TrasnaCellular/LEXI-ADAM-Arduino-shield-HW/shield_design_library/3D/DRL0006A.stp

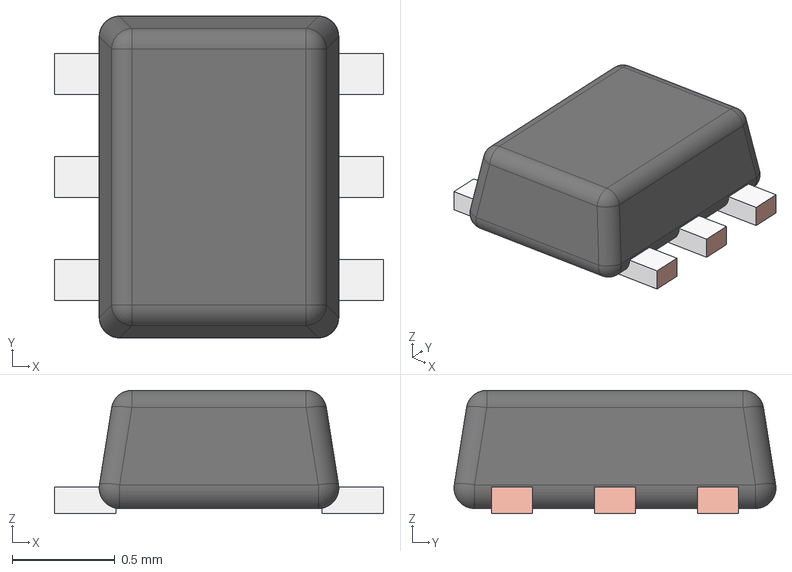
[picture p16: CAD file, 2026-05-26]
shield_design_library/3D/DRL0006A.stp
1.60 x 1.57 x 0.6 mm
FRAME-DRL0006A
BODY-SOT
PIN1-ID
