TrasnaCellular/LEXI-ADAM-Arduino-shield-HW/shield_design_library/3D/RES_SMA-A0102FTDL10R_TEC.step

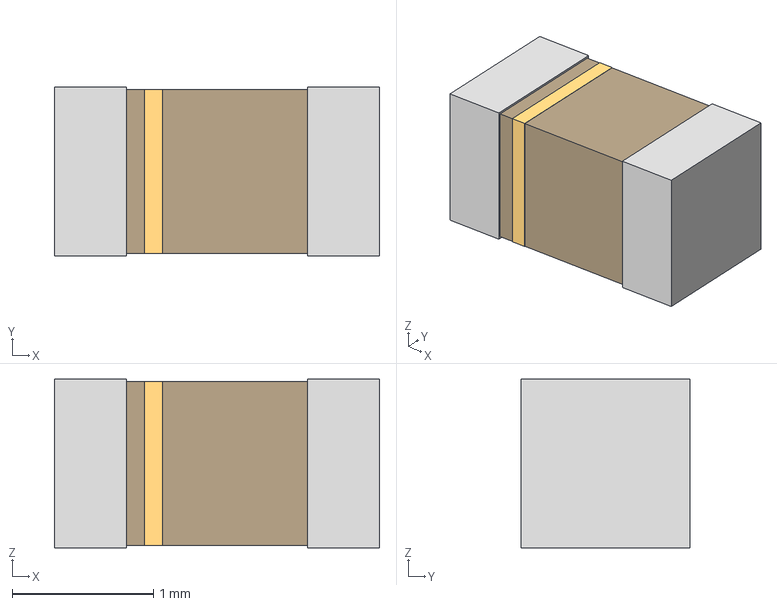
[picture p17: CAD file, 2026-05-26]
shield_design_library/3D/RES_SMA-A0102FTDL10R_TEC.step
2.30 x 1.19 x 1.19 mm
