TrasnaCellular/LEXI-ADAM-Arduino-shield-HW/shield_design_library/3D/SSW-106-03-G-S.stp

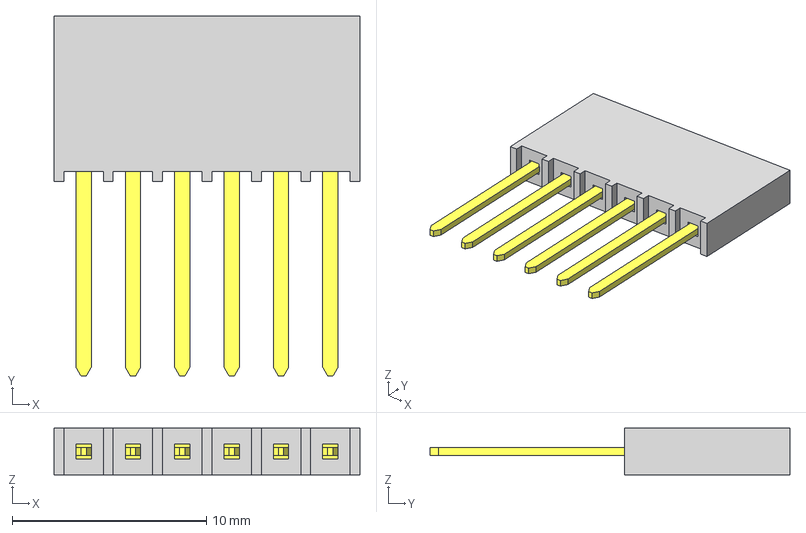
[picture p18: CAD file, 2026-05-26]
shield_design_library/3D/SSW-106-03-G-S.stp
15.7 x 18.5 x 2.41 mm
T1SSW-106-03-L-S
P2SSW-106-03-L-S
