TrasnaCellular/LEXI-ADAM-Arduino-shield-HW/shield_design_library/3D/Crystal_SMD_Abracon_ABM3B-4Pin_5.0x3.2mm.step

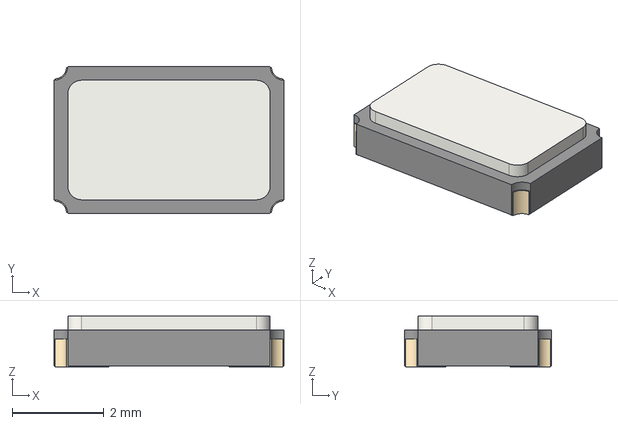
[picture p19: CAD file, 2026-05-26]
shield_design_library/3D/Crystal_SMD_Abracon_ABM3B-4Pin_5.0x3.2mm.step
5.00 x 3.20 x 1.10 mm
