TrasnaCellular/LEXI-ADAM-Arduino-shield-HW/shield_design_library/3D/IND_BLM18_0603_MUR.step

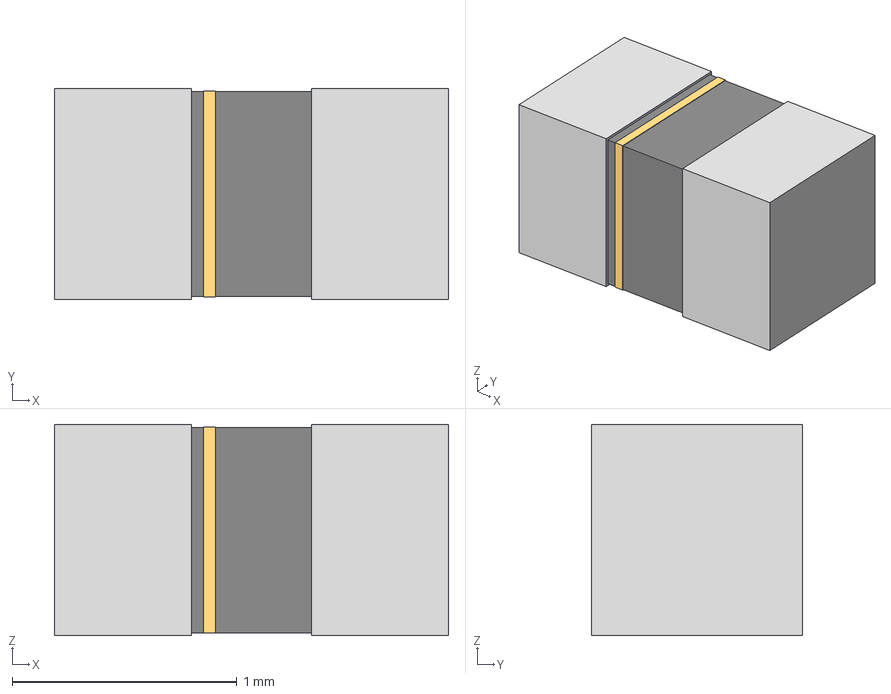
[picture p20: CAD file, 2026-05-26]
shield_design_library/3D/IND_BLM18_0603_MUR.step
1.75 x 0.94 x 0.94 mm
