TrasnaCellular/LEXI-ADAM-Arduino-shield-HW/shield_design_library/3D/LED_LTST-C190_LTO.step

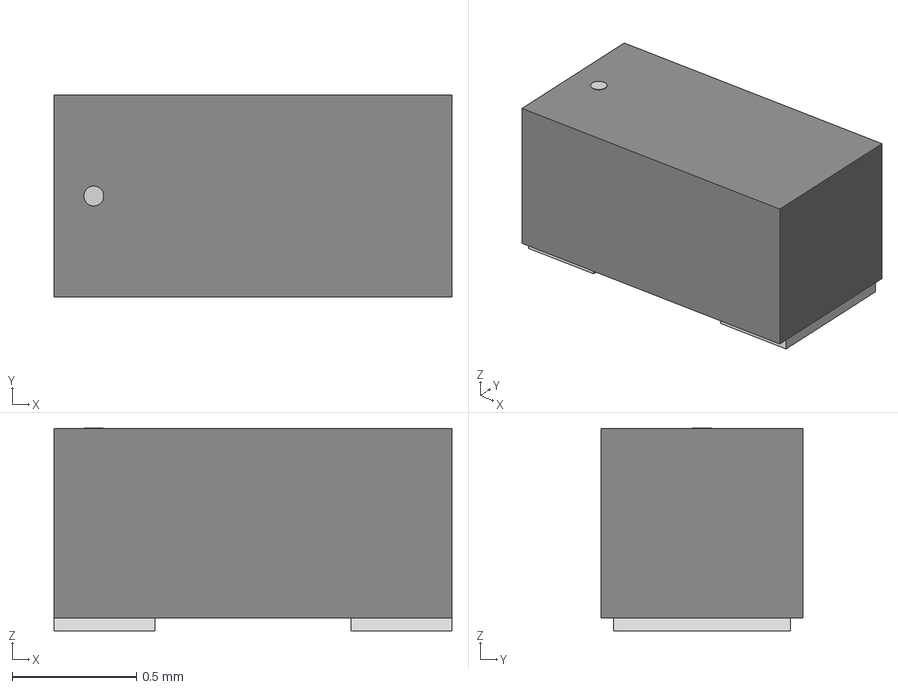
[picture p21: CAD file, 2026-05-26]
shield_design_library/3D/LED_LTST-C190_LTO.step
1.60 x 0.812 x 0.815 mm
