TrasnaCellular/LEXI-ADAM-Arduino-shield-HW/shield_design_library/3D/MICROPAK6_1X1P45_ONS.step

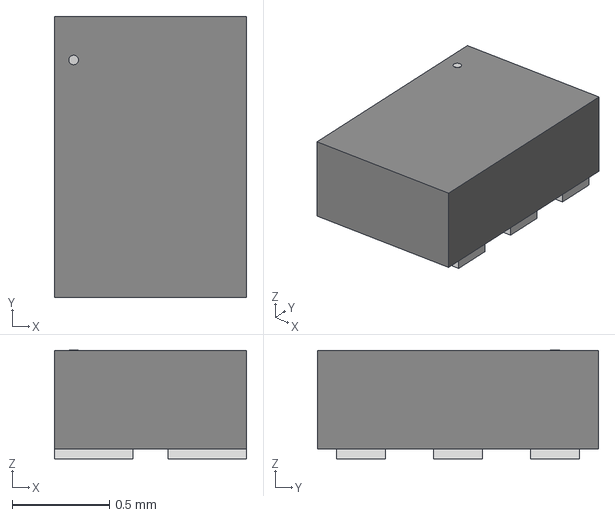
[picture p22: CAD file, 2026-05-26]
shield_design_library/3D/MICROPAK6_1X1P45_ONS.step
0.99 x 1.45 x 0.561 mm
