TrasnaCellular/LEXI-ADAM-Arduino-shield-HW/shield_design_library/3D/PESD0402-140_LTF.step

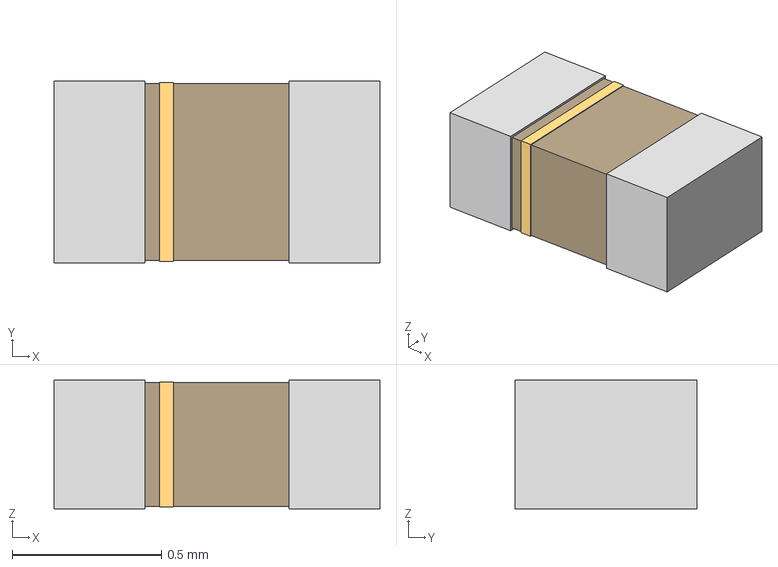
[picture p23: CAD file, 2026-05-26]
shield_design_library/3D/PESD0402-140_LTF.step
1.09 x 0.61 x 0.432 mm
