TrasnaCellular/LEXI-ADAM-Arduino-shield-HW/shield_design_library/3D/21-0076E_MXM.step

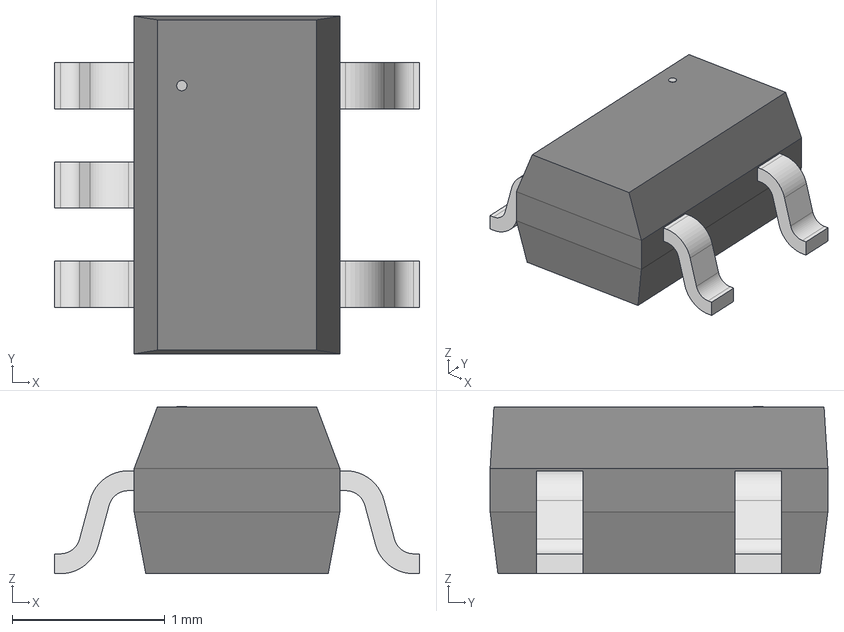
[picture p24: CAD file, 2026-05-26]
shield_design_library/3D/21-0076E_MXM.step
2.39 x 2.21 x 1.09 mm
