TrasnaCellular/LEXI-ADAM-Arduino-shield-HW/shield_design_library/3D/CT3151-0.stp

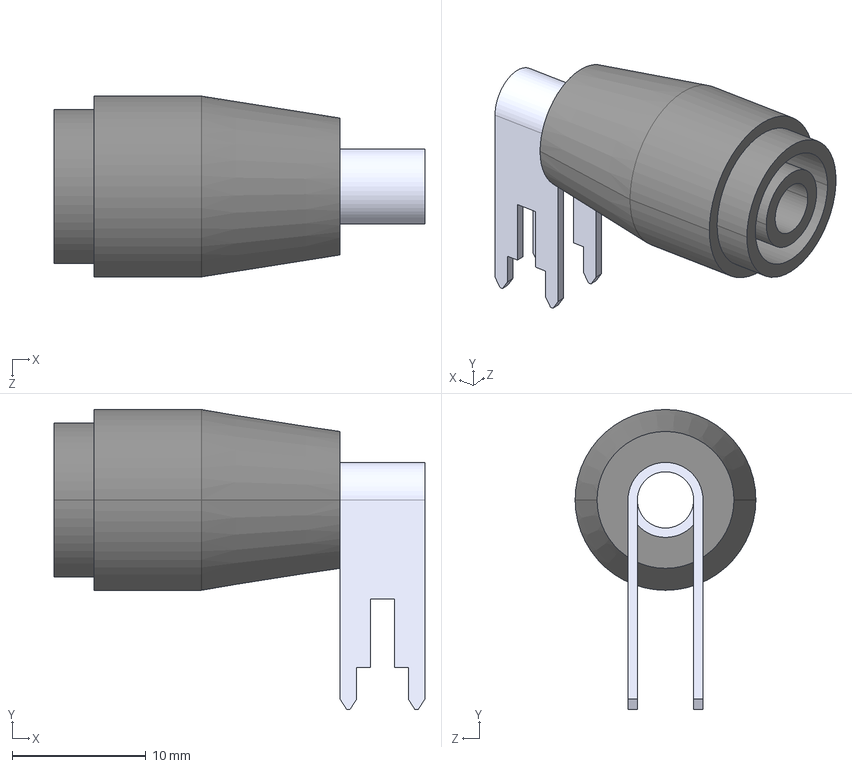
[picture p25: CAD file, 2026-05-26]
shield_design_library/3D/CT3151-0.stp
27.7 x 22.4 x 13.5 mm
