TrasnaCellular/LEXI-ADAM-Arduino-shield-HW/shield_design_library/3D/SC-88A-5_1P35X2P2_ONS.step

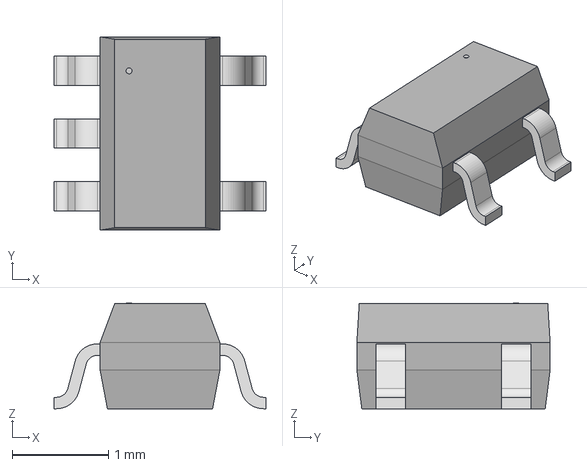
[picture p26: CAD file, 2026-05-26]
shield_design_library/3D/SC-88A-5_1P35X2P2_ONS.step
2.20 x 2.01 x 1.09 mm
