TrasnaCellular/LEXI-ADAM-Arduino-shield-HW/shield_design_library/3D/SOT-23-5_ONS.step

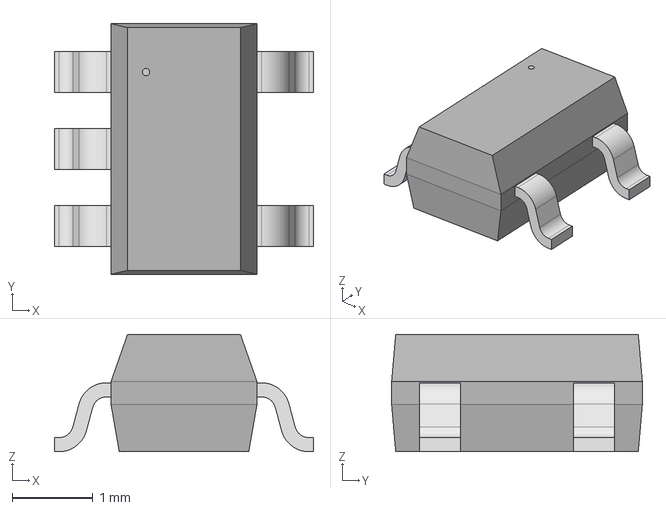
[picture p27: CAD file, 2026-05-26]
shield_design_library/3D/SOT-23-5_ONS.step
3.20 x 3.10 x 1.45 mm
