TrasnaCellular/LEXI-ADAM-Arduino-shield-HW/shield_design_library/3D/RES_SLN5_KOA.step

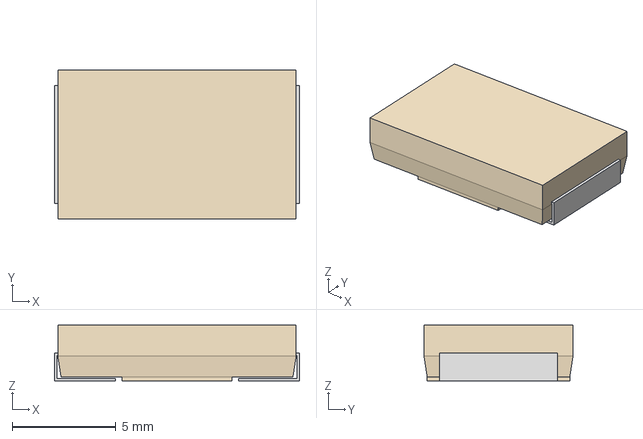
[picture p28: CAD file, 2026-05-26]
shield_design_library/3D/RES_SLN5_KOA.step
11.8 x 7.19 x 2.69 mm
