TrasnaCellular/LEXI-ADAM-Arduino-shield-HW/shield_design_library/3D/LTST-C190KRKT.stp

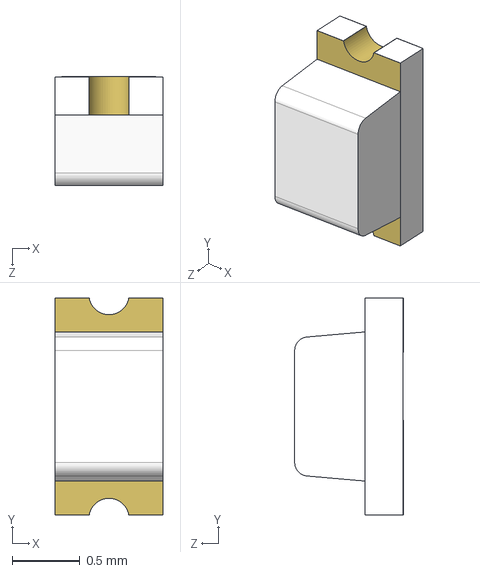
[picture p29: CAD file, 2026-05-26]
shield_design_library/3D/LTST-C190KRKT.stp
0.8 x 1.60 x 0.801 mm
