TrasnaCellular/LEXI-ADAM-Arduino-shield-HW/shield_design_library/3D/IND_BLM15_0402_MUR.step

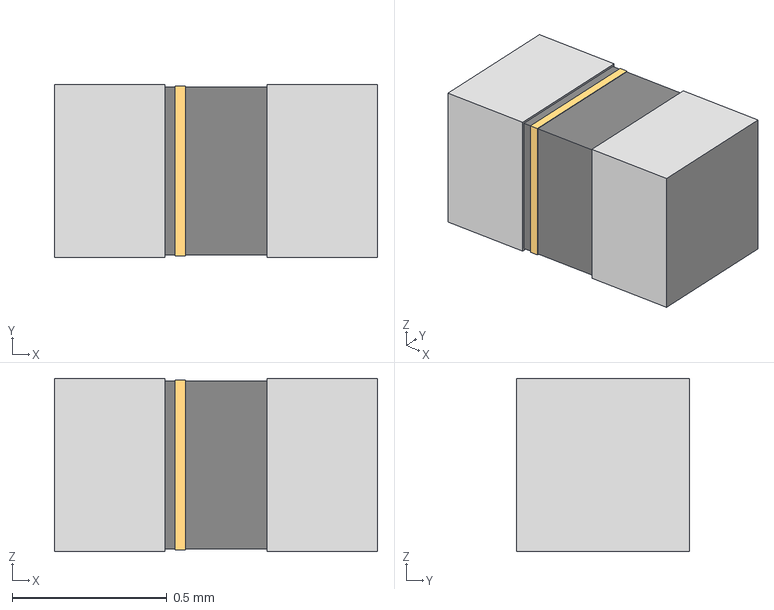
[picture p30: CAD file, 2026-05-26]
shield_design_library/3D/IND_BLM15_0402_MUR.step
1.04 x 0.558 x 0.559 mm
