TrasnaCellular/LEXI-ADAM-Arduino-shield-HW/shield_design_library/3D/TPSM828303ARDSR.stp

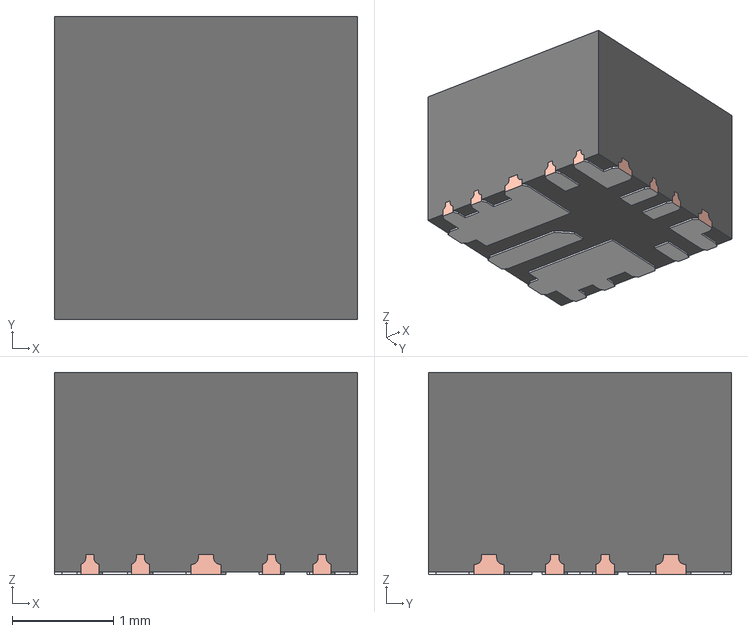
[picture p31: CAD file, 2026-05-26]
shield_design_library/3D/TPSM828303ARDSR.stp
3.00 x 3.00 x 2.00 mm
RDS0009A_FRAME
RDS0009A_MOLD
