TrasnaCellular/LEXI-ADAM-Arduino-shield-HW/shield_design_library/3D/RJ_6_ADI.step

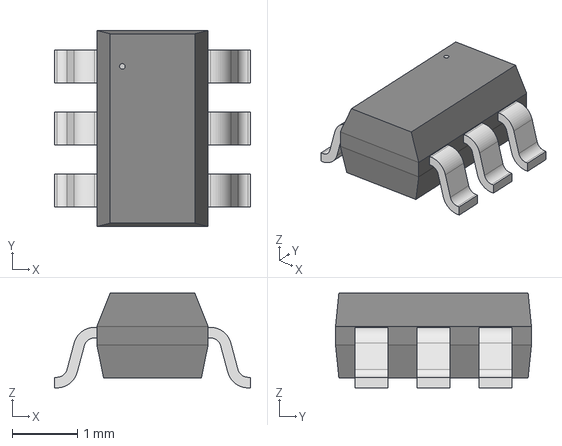
[picture p32: CAD file, 2026-05-26]
shield_design_library/3D/RJ_6_ADI.step
3.00 x 3.00 x 1.45 mm
