TrasnaCellular/LEXI-ADAM-Arduino-shield-HW/shield_design_library/3D/QFN32_5X5MC_MCH.step

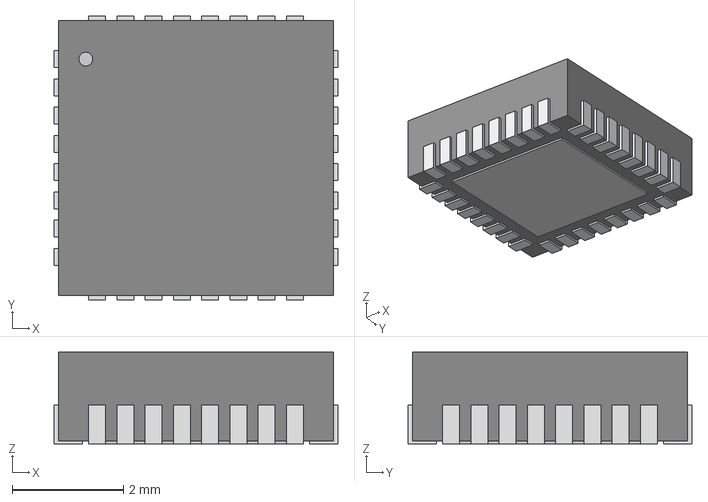
[picture p33: CAD file, 2026-05-26]
shield_design_library/3D/QFN32_5X5MC_MCH.step
5.11 x 5.11 x 1.65 mm
