TrasnaCellular/LEXI-ADAM-Arduino-shield-HW/shield_design_library/3D/PBS0032A.stp

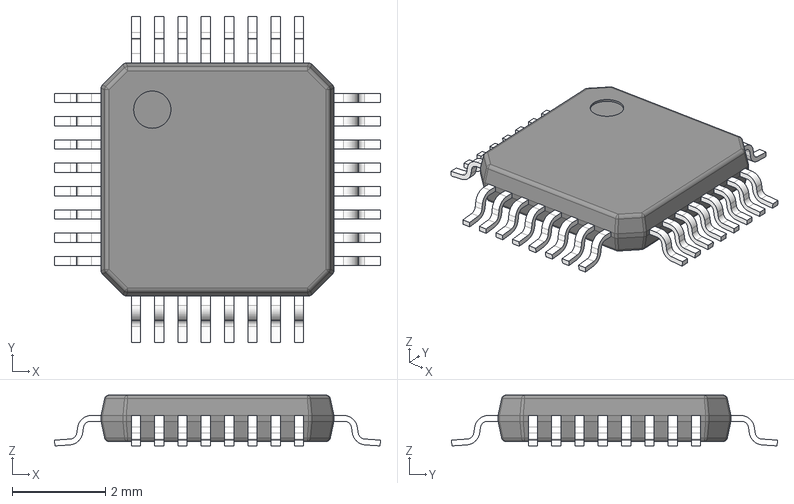
[picture p34: CAD file, 2026-05-26]
shield_design_library/3D/PBS0032A.stp
7.00 x 7.00 x 1.09 mm
BODY-TQFP
LEAD-TQFP x 32
PIN1
