TrasnaCellular/LEXI-ADAM-Arduino-shield-HW/shield_design_library/3D/DGK0008A.stp

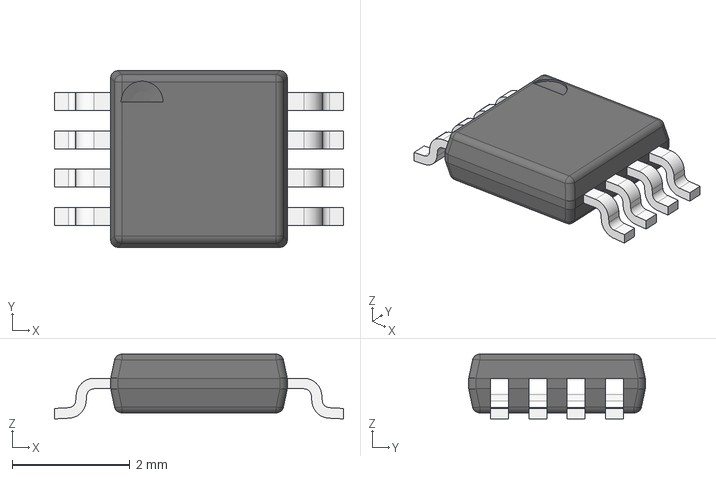
[picture p35: CAD file, 2026-05-26]
shield_design_library/3D/DGK0008A.stp
4.90 x 3.00 x 1.10 mm
BODY_MUA08A
LEAD_MUA08A x 8
