TrasnaCellular/LEXI-ADAM-Arduino-shield-HW/shield_design_library/3D/DDA0008J.stp

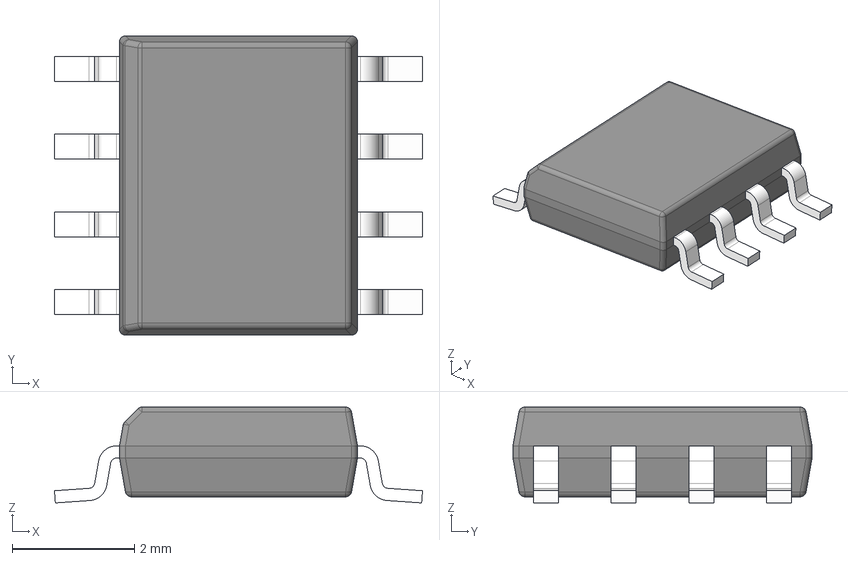
[picture p36: CAD file, 2026-05-26]
shield_design_library/3D/DDA0008J.stp
6.03 x 4.90 x 1.57 mm
BODY-SO
LEAD-SO x 8
THERMALPAD-SO
