TrasnaCellular/LEXI-ADAM-Arduino-shield-HW/shield_design_library/3D/IND_IFSC-2020DE-01_VIS.step

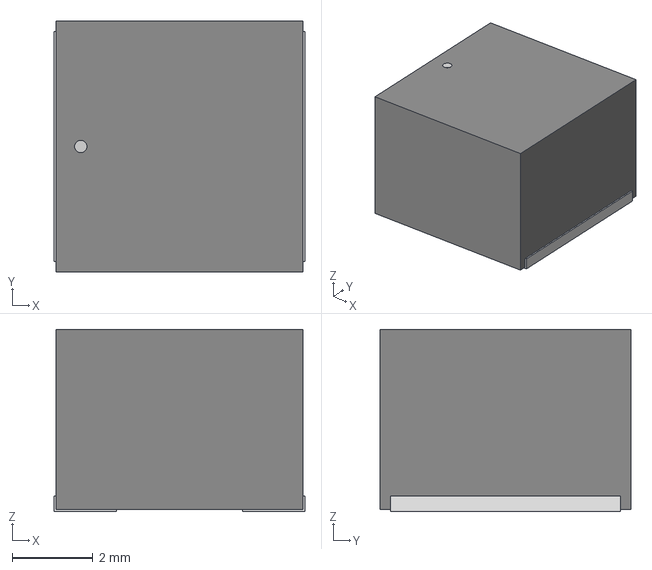
[picture p37: CAD file, 2026-05-26]
shield_design_library/3D/IND_IFSC-2020DE-01_VIS.step
6.20 x 6.20 x 4.50 mm
