TrasnaCellular/LEXI-ADAM-Arduino-shield-HW/shield_design_library/3D/DCK0005A.stp

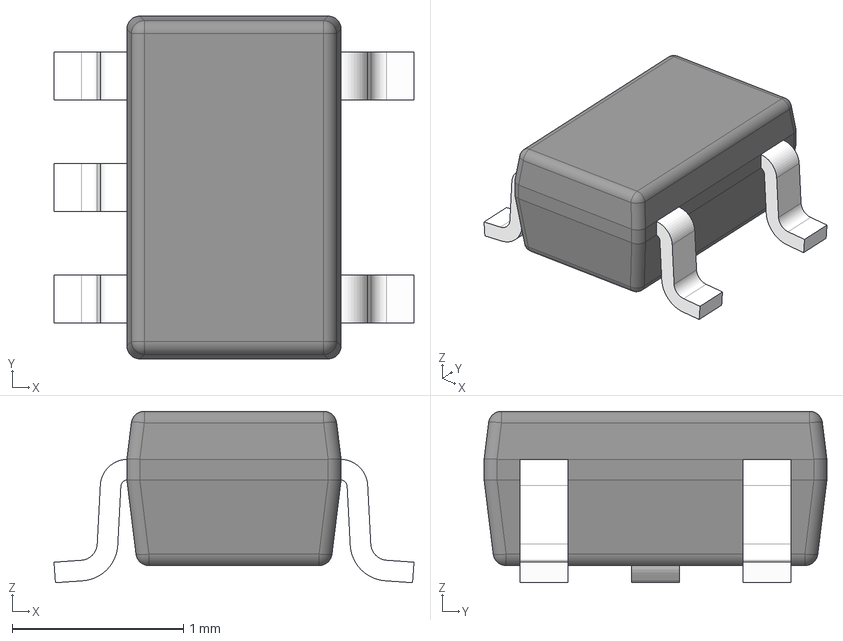
[picture p38: CAD file, 2026-05-26]
shield_design_library/3D/DCK0005A.stp
2.10 x 2.00 x 1.00 mm
BODY-SOT
LEAD-SOT x 5
PIN1-ID
